sephiroth74/esp32-calendar/kicad/esp32-calendar/esp32-calendar.kicad_sch

## KiCad design kicad/esp32-calendar/esp32-calendar.kicad_sch (2025-11-11, an earlier design)

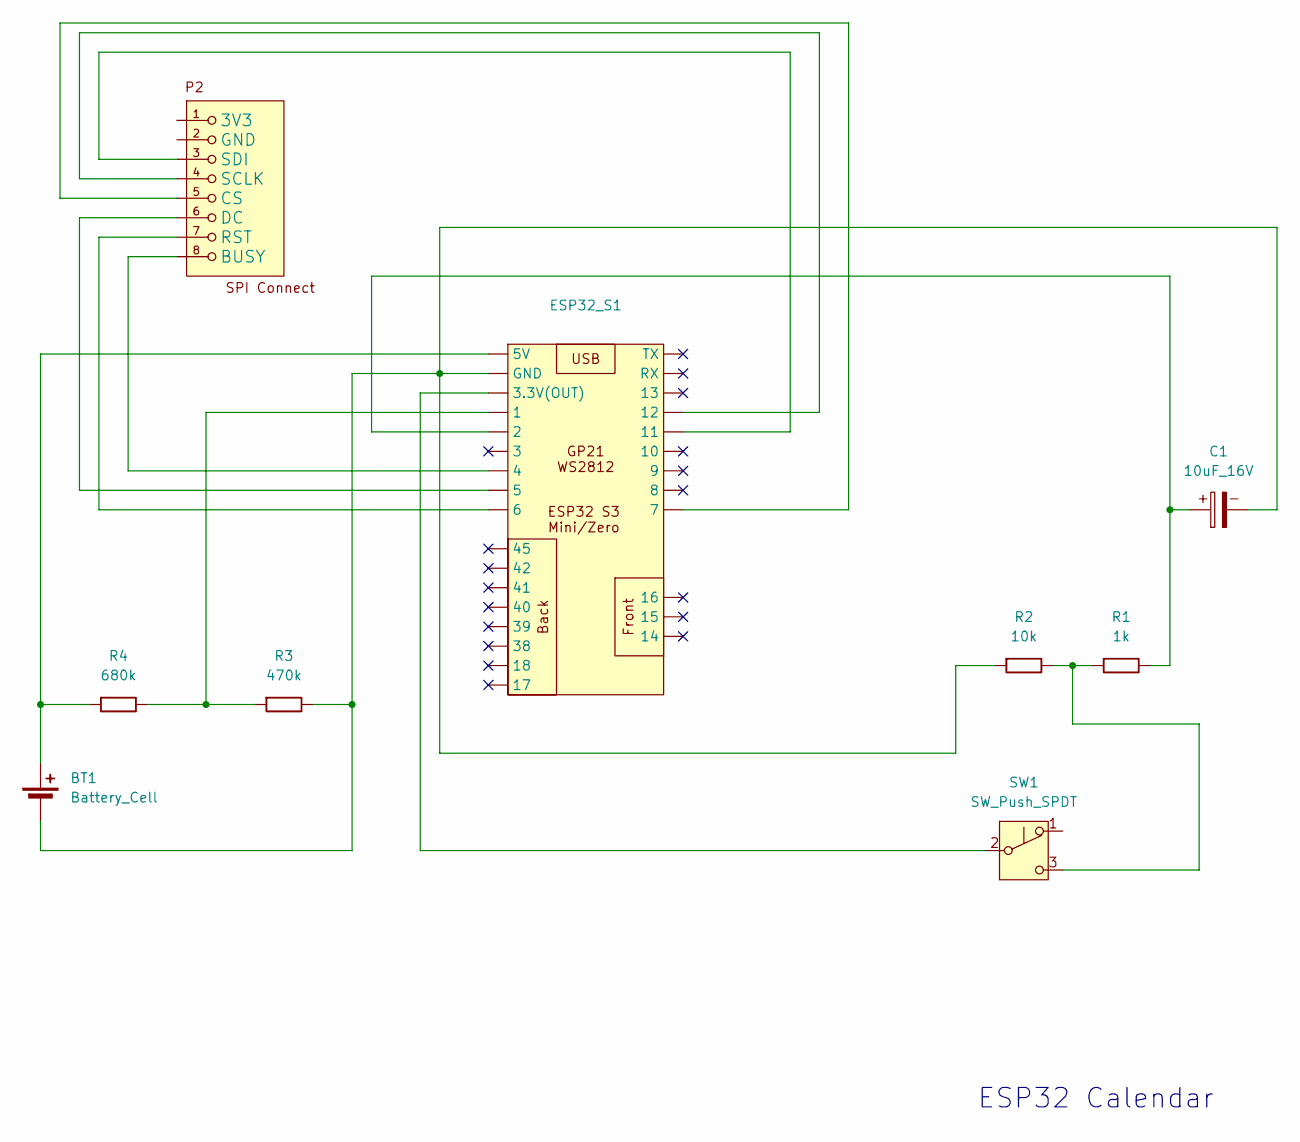
[picture p5: schematic esp32-calendar.kicad_sch]

Parts:
BT1: Battery_Cell
C1: 10uF_16V; CP_Radial_D5.0mm_P2.00mm
ESP32_S1: (no value)
R1: 1k; R_Axial_DIN0207_L6.3mm_D2.5mm_P10.16mm_Horizontal
R2: 10k; R_Axial_DIN0207_L6.3mm_D2.5mm_P10.16mm_Horizontal
R3: 470k; R_Axial_DIN0207_L6.3mm_D2.5mm_P10.16mm_Horizontal
R4: 680k; R_Axial_DIN0207_L6.3mm_D2.5mm_P10.16mm_Horizontal
SW1: SW_Push_SPDT
U1: (no value)

Connections:
unnamed: BT1.1 (+), ESP32_S1., R4.1
unnamed: BT1.2 (-), C1.2, ESP32_S1., R2.1, R3.2
unnamed: C1.1, ESP32_S1., R1.2
unnamed: ESP32_S1., R3.1, R4.2, SW1.2 (B), U1.3 (SDI), U1.4 (SCLK), U1.5 (CS), U1.6 (DC), U1.7 (RST), U1.8 (BUSY)
unnamed: R1.1, R2.2, SW1.3 (C)

Notes on the sheet:
ESP32 Calendar
